takashicompany/dogtag/images/02.jpg

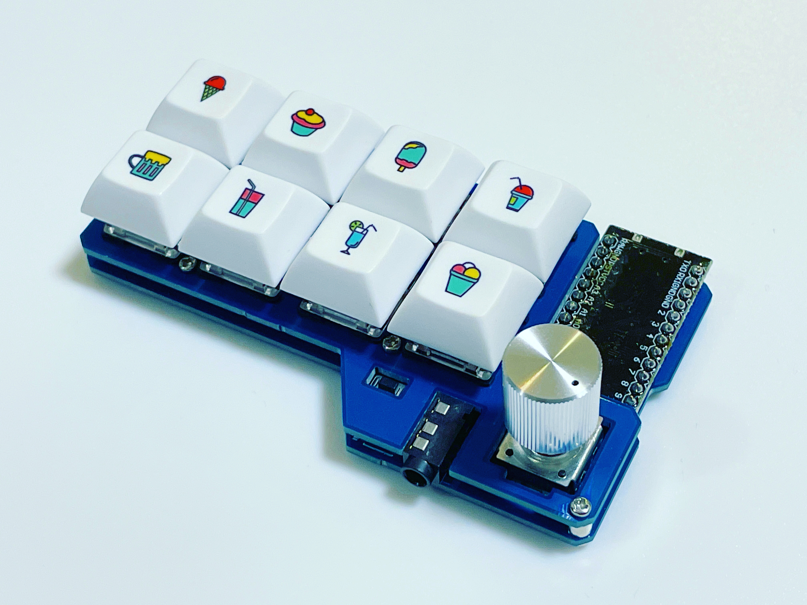
images/02.jpg
