takashicompany/dogtag/images/03.jpg

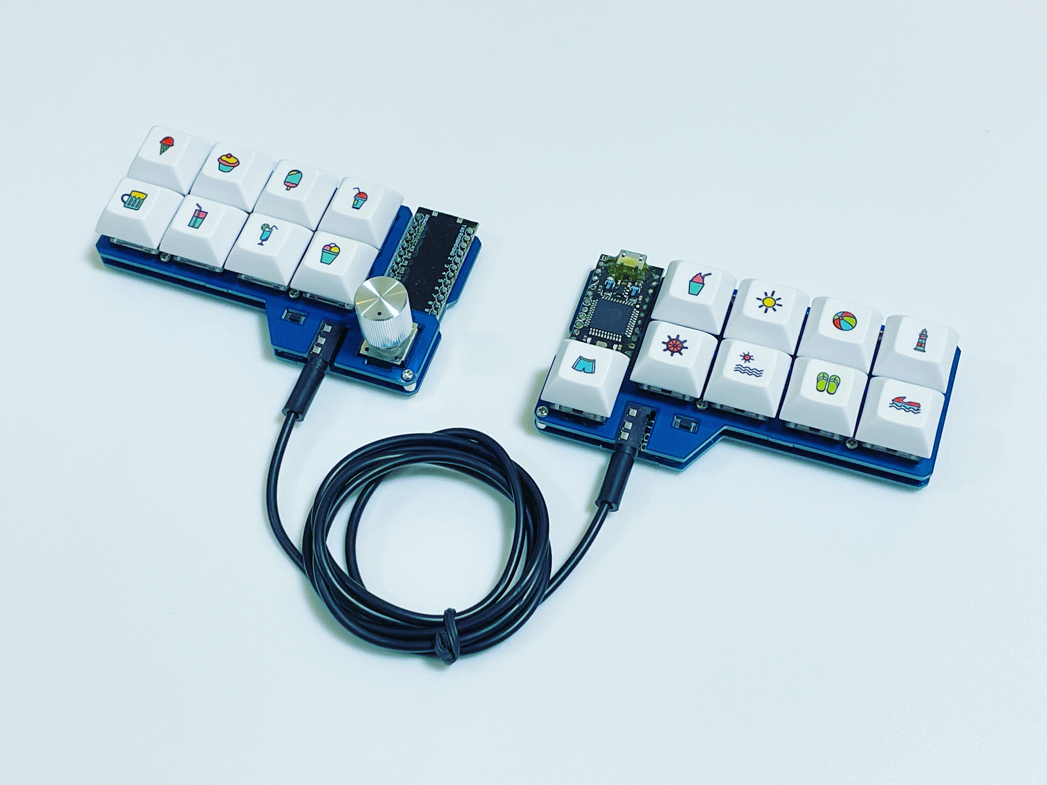
images/03.jpg
