takashicompany/dogtag/images/16.jpg

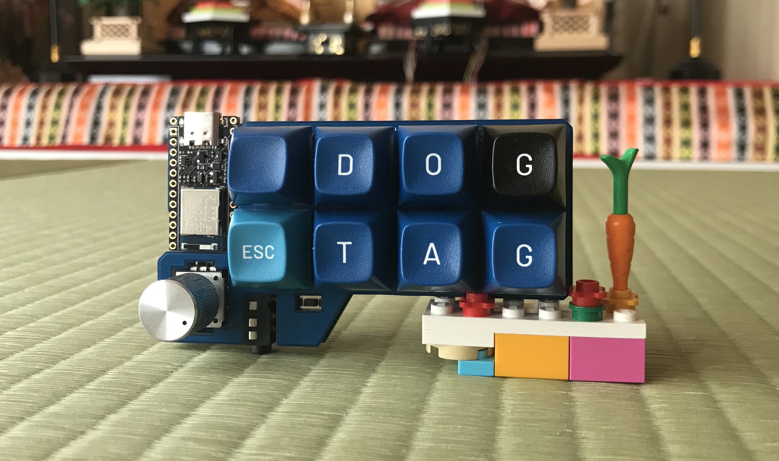
images/16.jpg
