takashicompany/dogtag/images/17.jpg

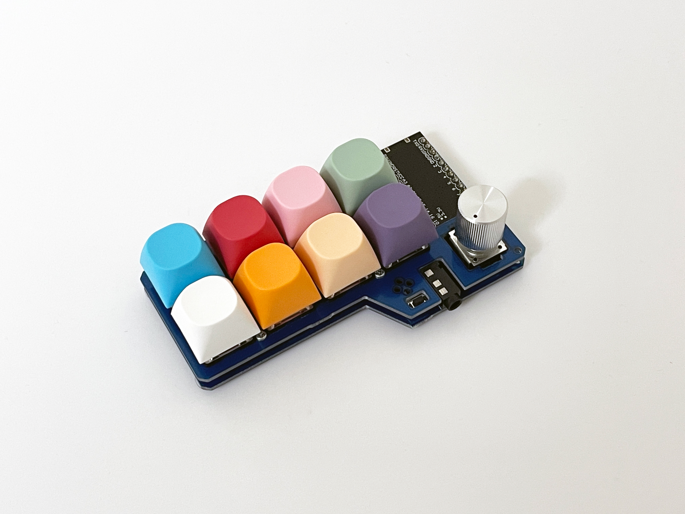
images/17.jpg
