takashicompany/dogtag/images/18.jpg

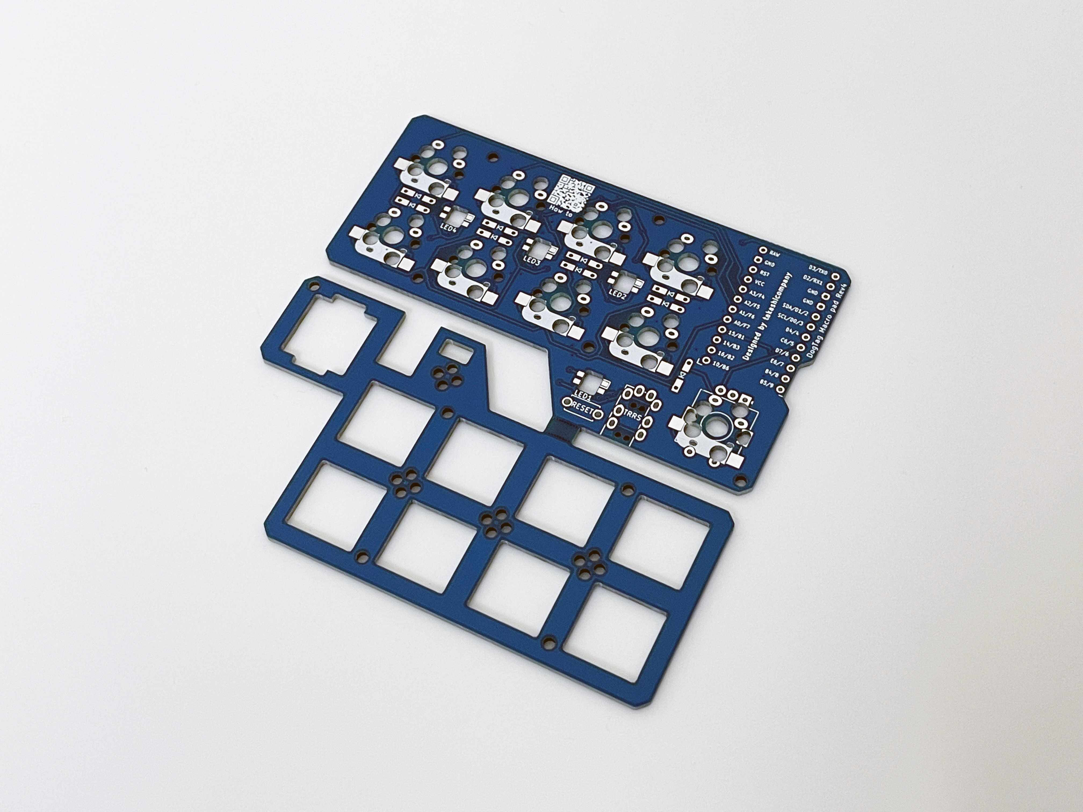
images/18.jpg
