takashicompany/dogtag/images/20.jpg

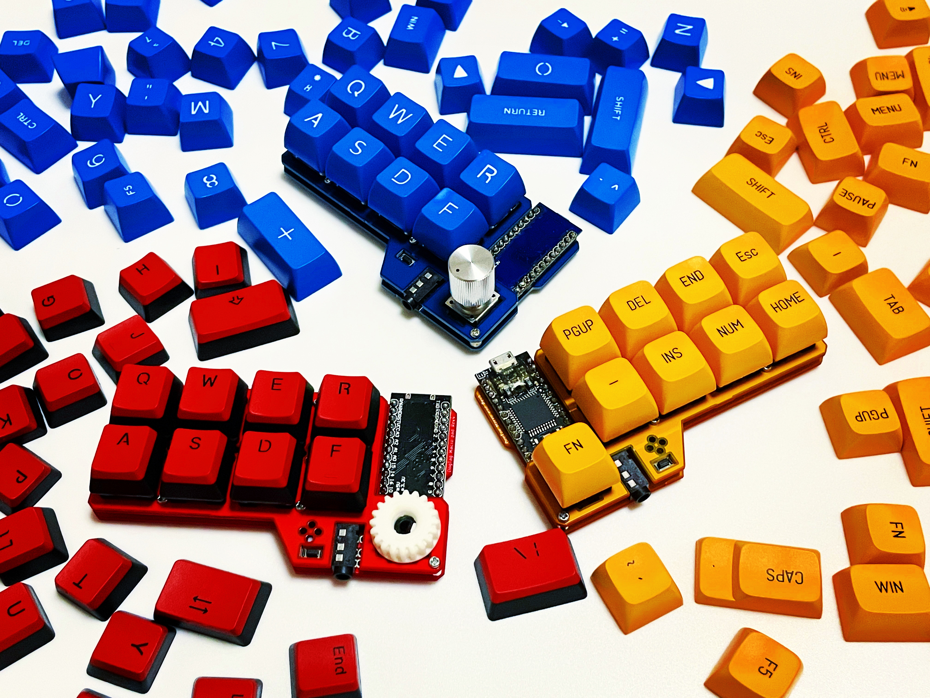
images/20.jpg
